RabiatS/MagicMitts/CAD Drawing/JN - Control Center/CC Proto K/JN - L1K Electromagnetic and String Housing.SLDPRT

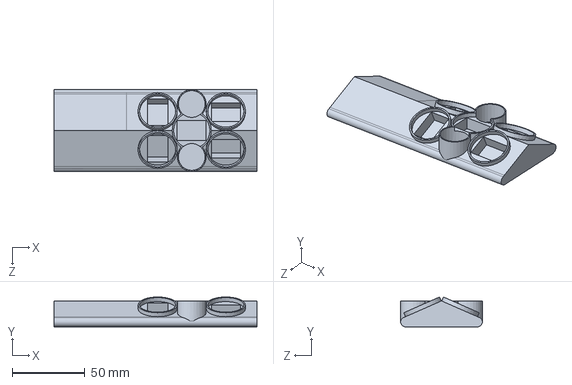
[picture p21: CAD file, 2025-01-15]
CAD Drawing/JN - Control Center/CC Proto K/JN - L1K Electromagnetic and String Housing.SLDPRT
140.0 x 20.7 x 56.4 mm
