RabiatS/MagicMitts/CAD Drawing/JN - Control Center/CC Proto L/JN - L1L Electromagnetic and String Housing.SLDPRT

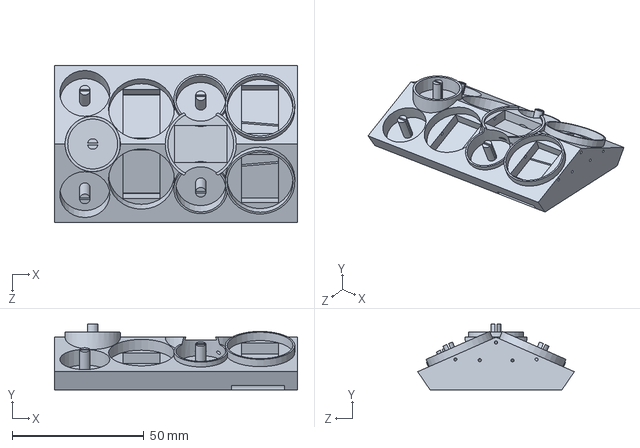
[picture p22: CAD file, 2025-01-15]
CAD Drawing/JN - Control Center/CC Proto L/JN - L1L Electromagnetic and String Housing.SLDPRT
92.2 x 25.0 x 59.4 mm
