RabiatS/MagicMitts/CAD Drawing/JN - Control Center/CC Proto M/JN - L1M Electromagnetic and String Housing.SLDPRT

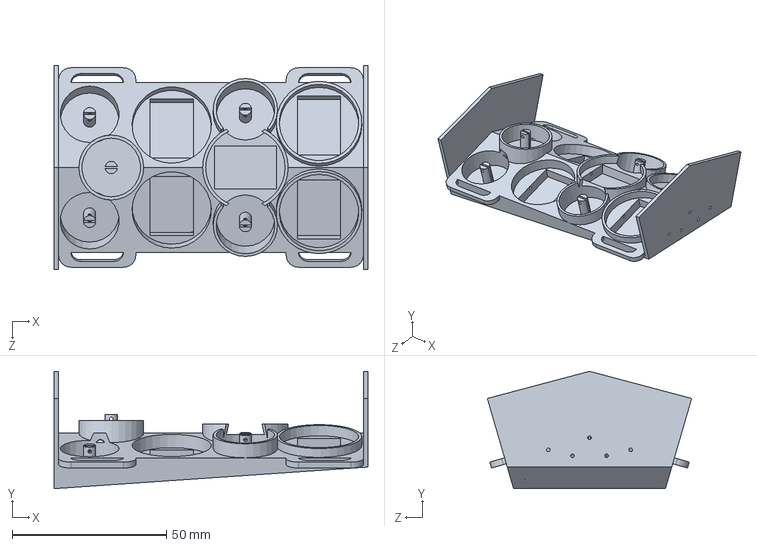
[picture p23: CAD file, 2025-01-15]
CAD Drawing/JN - Control Center/CC Proto M/JN - L1M Electromagnetic and String Housing.SLDPRT
101.7 x 38.0 x 66.2 mm
