RabiatS/MagicMitts/CAD Drawing/JN - Finger Caps and Tracks/JN - FCT Proto A/JN - Top Finger Cap - TFC-A.SLDPRT

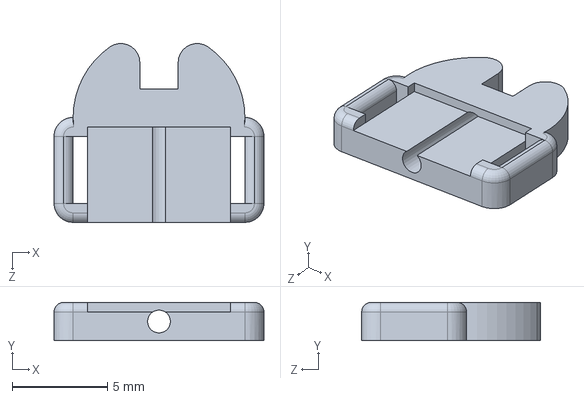
[picture p24: CAD file, 2025-01-15]
CAD Drawing/JN - Finger Caps and Tracks/JN - FCT Proto A/JN - Top Finger Cap - TFC-A.SLDPRT
11.0 x 2.00 x 9.37 mm
