RabiatS/MagicMitts/CAD Drawing/JN - Finger Caps and Tracks/JN - FCT Proto B/JN - Flex String Track - FST-B.SLDPRT

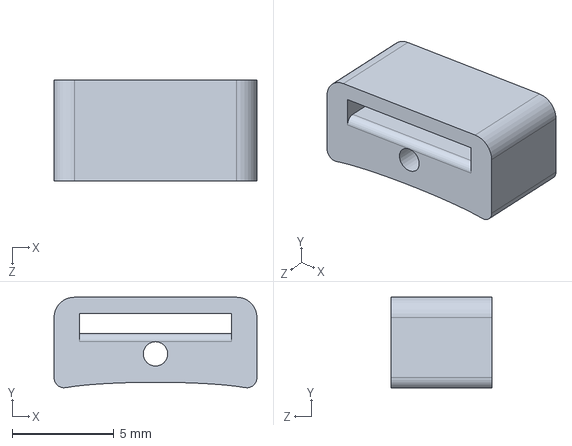
[picture p25: CAD file, 2025-01-15]
CAD Drawing/JN - Finger Caps and Tracks/JN - FCT Proto B/JN - Flex String Track - FST-B.SLDPRT
10.0 x 4.46 x 5.00 mm
