RabiatS/MagicMitts/CAD Drawing/JN - Reel Component Testing/JN - RC Testing 2/JN - Reel Caps Size2 T2.SLDPRT

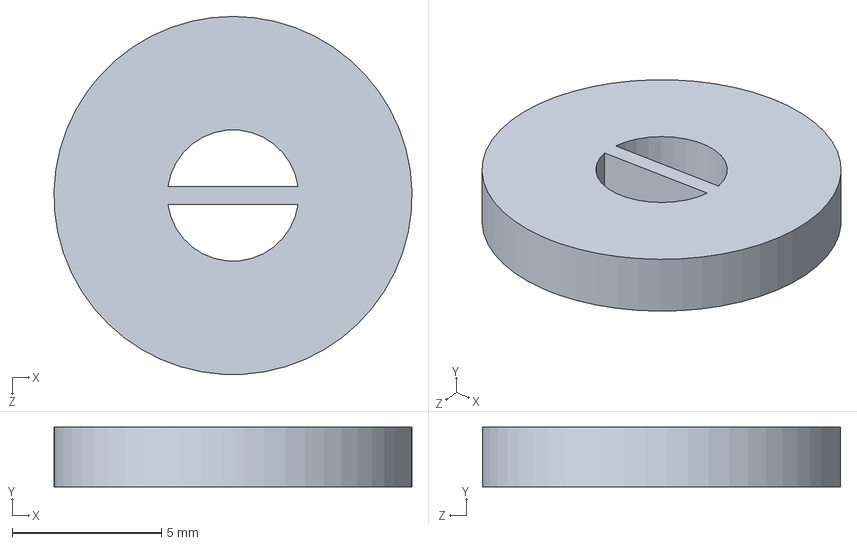
[picture p27: CAD file, 2025-01-15]
CAD Drawing/JN - Reel Component Testing/JN - RC Testing 2/JN - Reel Caps Size2 T2.SLDPRT
12.0 x 2.00 x 12.0 mm
