RabiatS/MagicMitts/CAD Drawing/BN - Battery Pack/BN - BP Proto A/BN - BP_BOTTOM A.STL

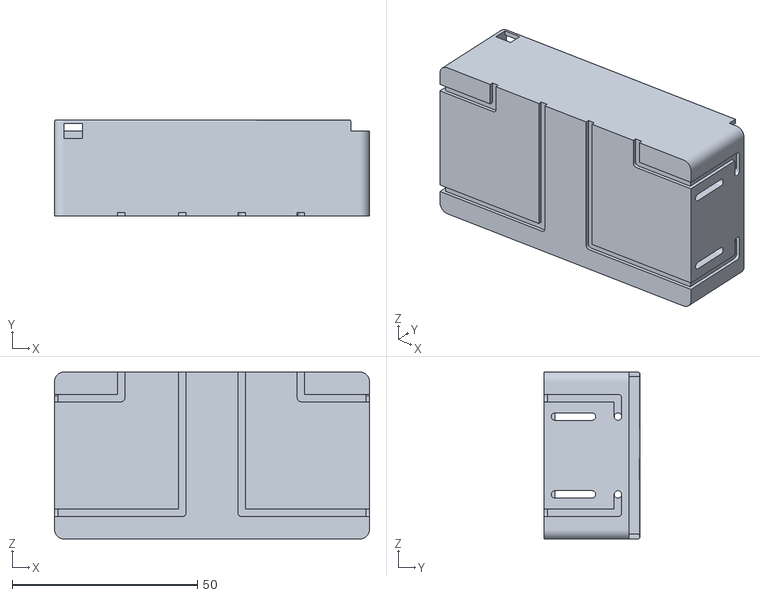
[picture p28: CAD file, 2025-01-15]
CAD Drawing/BN - Battery Pack/BN - BP Proto A/BN - BP_BOTTOM A.STL
85.0 x 26.0 x 45.0
