RabiatS/MagicMitts/CAD Drawing/BN - Battery Pack/BN - BP Proto B/BN - BP_LID B.STL

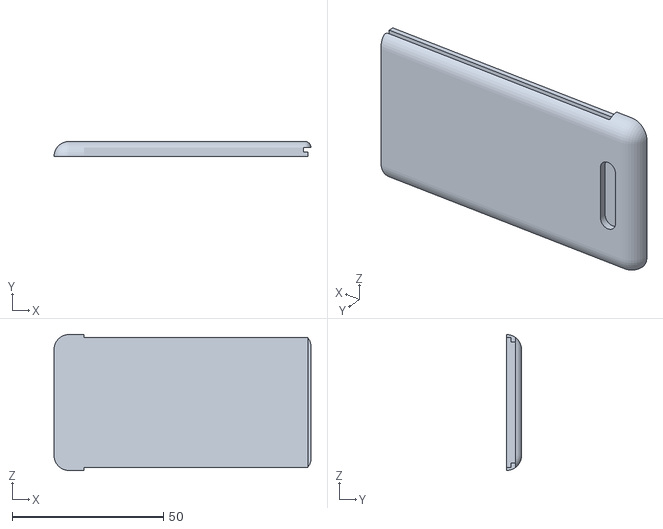
[picture p29: CAD file, 2025-01-15]
CAD Drawing/BN - Battery Pack/BN - BP Proto B/BN - BP_LID B.STL
85.0 x 5.00 x 45.0
