RabiatS/MagicMitts/CAD Drawing/JN - Ball Bearing Testing/JN - BB Testing 1/JN - Pole Size Testing Plate.SLDPRT

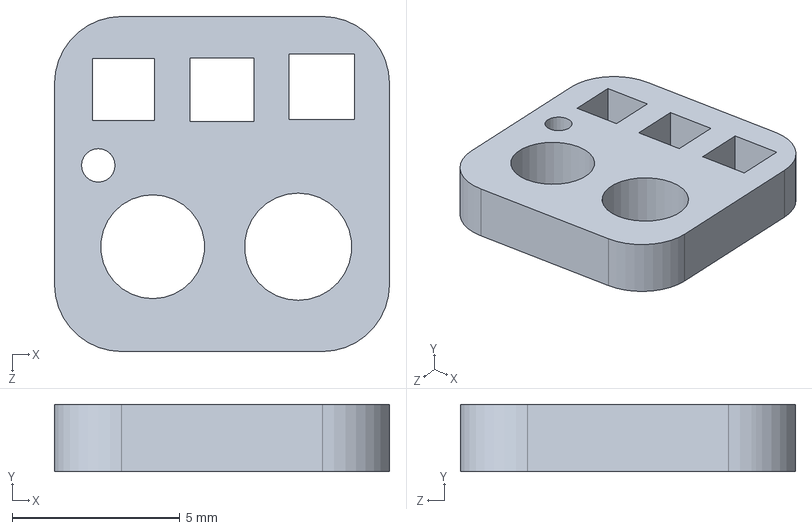
[picture p30: CAD file, 2025-01-15]
CAD Drawing/JN - Ball Bearing Testing/JN - BB Testing 1/JN - Pole Size Testing Plate.SLDPRT
10.00 x 2.00 x 10.0 mm
