RabiatS/MagicMitts/CAD Drawing/JN - Control Center/CC Proto B/JN - L3B Electromagnetic Housing Cap.SLDPRT

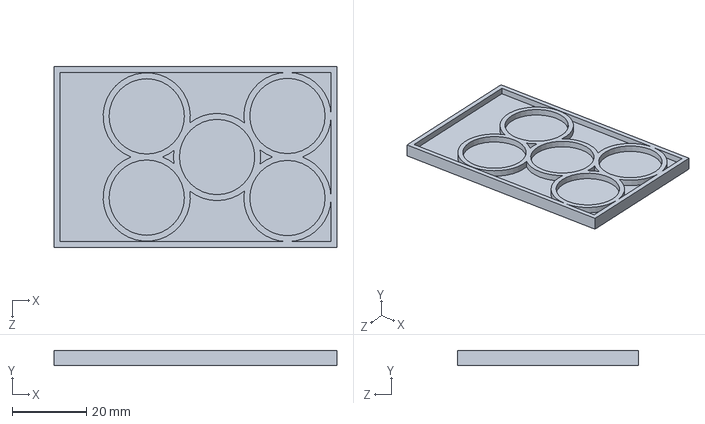
[picture p31: CAD file, 2025-01-15]
CAD Drawing/JN - Control Center/CC Proto B/JN - L3B Electromagnetic Housing Cap.SLDPRT
76.0 x 4.00 x 48.7 mm
