RabiatS/MagicMitts/CAD Drawing/JN - Control Center/CC Proto C/JN - TP L1C Electromagnetic and String.SLDPRT

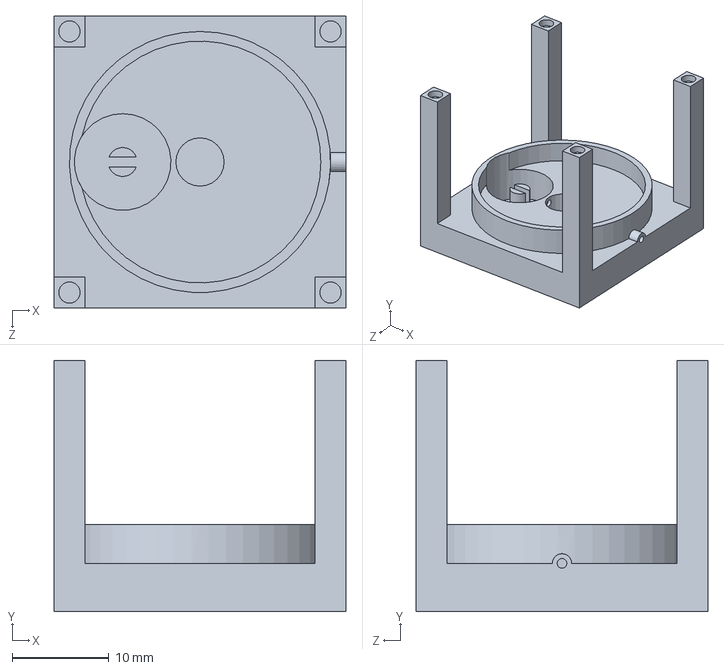
[picture p32: CAD file, 2025-01-15]
CAD Drawing/JN - Control Center/CC Proto C/JN - TP L1C Electromagnetic and String.SLDPRT
30.2 x 26.0 x 30.2 mm
