RabiatS/MagicMitts/CAD Drawing/JN - Control Center/CC Proto D/JN - LD Badge Reel Component.SLDPRT

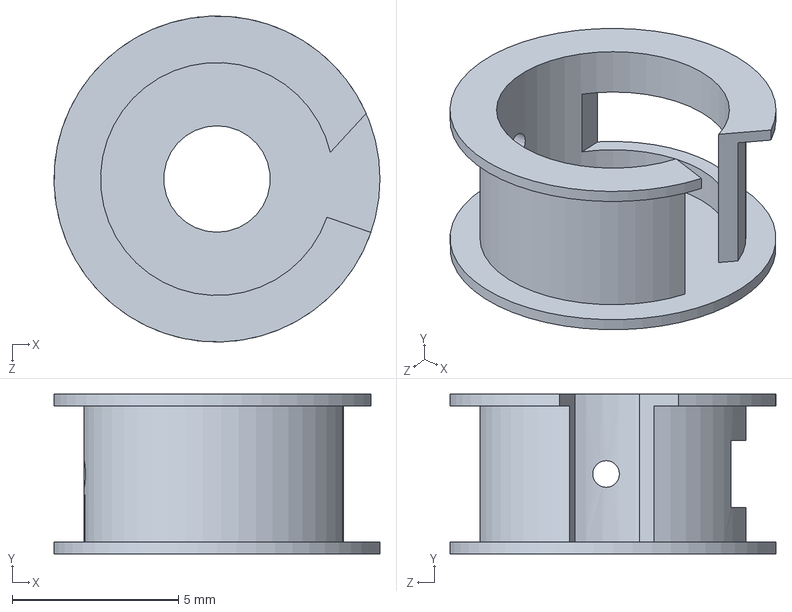
[picture p33: CAD file, 2025-01-15]
CAD Drawing/JN - Control Center/CC Proto D/JN - LD Badge Reel Component.SLDPRT
9.80 x 4.80 x 9.80 mm
