RabiatS/MagicMitts/CAD Drawing/JN - Control Center/CC Proto E/JN - TP L1E Electromagnetic and String Housing.SLDPRT

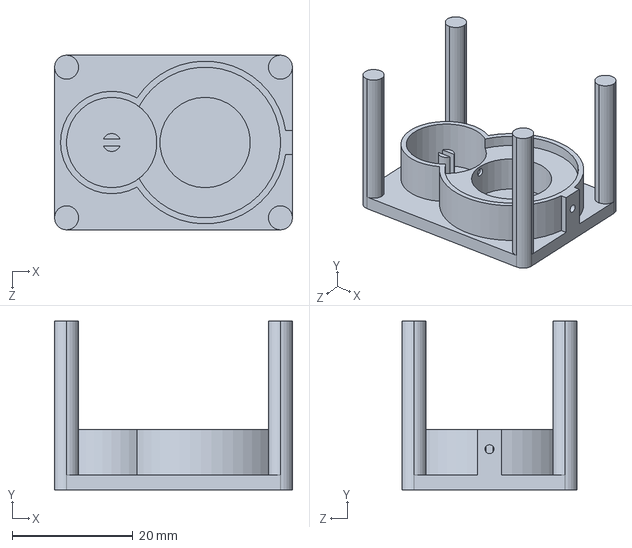
[picture p34: CAD file, 2025-01-15]
CAD Drawing/JN - Control Center/CC Proto E/JN - TP L1E Electromagnetic and String Housing.SLDPRT
39.5 x 28.0 x 29.0 mm
