RabiatS/MagicMitts/CAD Drawing/JN - Control Center/CC Proto G/JN - TP L2G Cap.SLDPRT

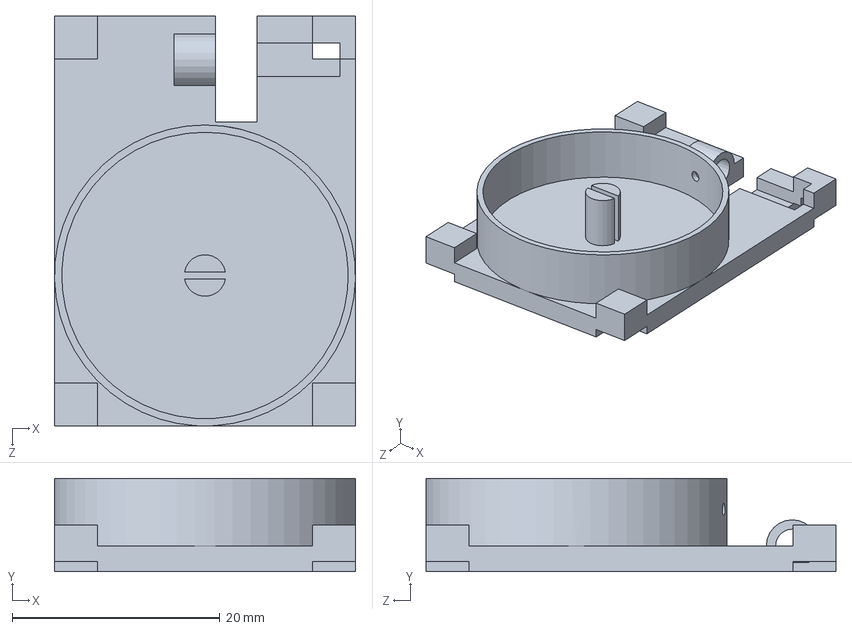
[picture p35: CAD file, 2025-01-15]
CAD Drawing/JN - Control Center/CC Proto G/JN - TP L2G Cap.SLDPRT
29.0 x 9.00 x 39.5 mm
