RabiatS/MagicMitts/CAD Drawing/JN - Control Center/CC Proto H/JN - TP L1H Badge Reel Cap.SLDPRT

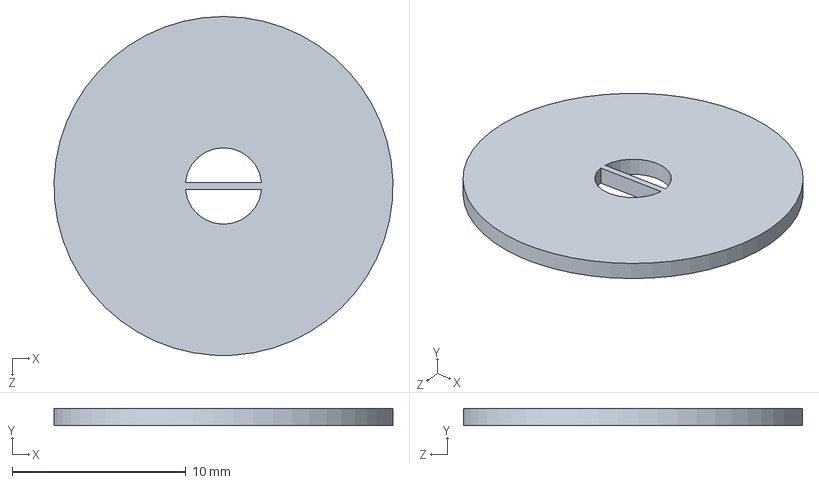
[picture p36: CAD file, 2025-01-15]
CAD Drawing/JN - Control Center/CC Proto H/JN - TP L1H Badge Reel Cap.SLDPRT
19.5 x 1.00 x 19.5 mm
