RabiatS/MagicMitts/CAD Drawing/JN - Control Center/CC Proto J/JN - L1J Electromagnetic and String Housing.SLDPRT

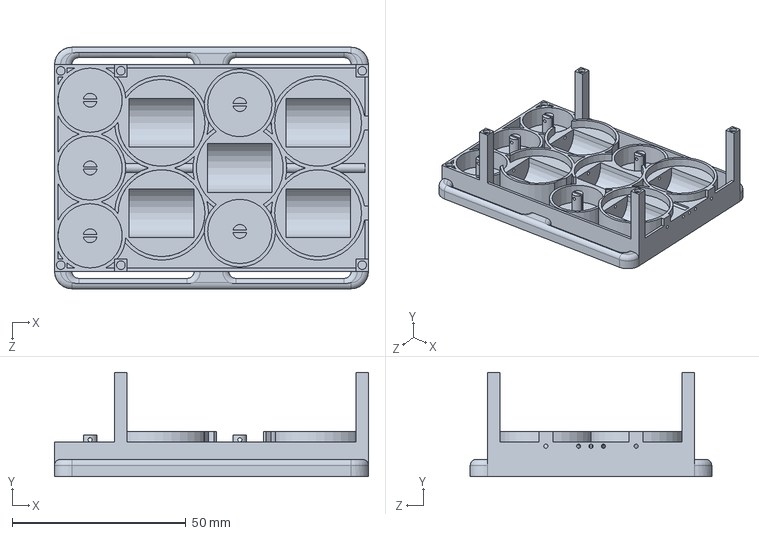
[picture p37: CAD file, 2025-01-15]
CAD Drawing/JN - Control Center/CC Proto J/JN - L1J Electromagnetic and String Housing.SLDPRT
90.3 x 30.0 x 69.5 mm
