RabiatS/MagicMitts/CAD Drawing/JN - Finger Caps and Tracks/JN - FCT Proto A/JN - Flex String Track - FST-A.SLDPRT

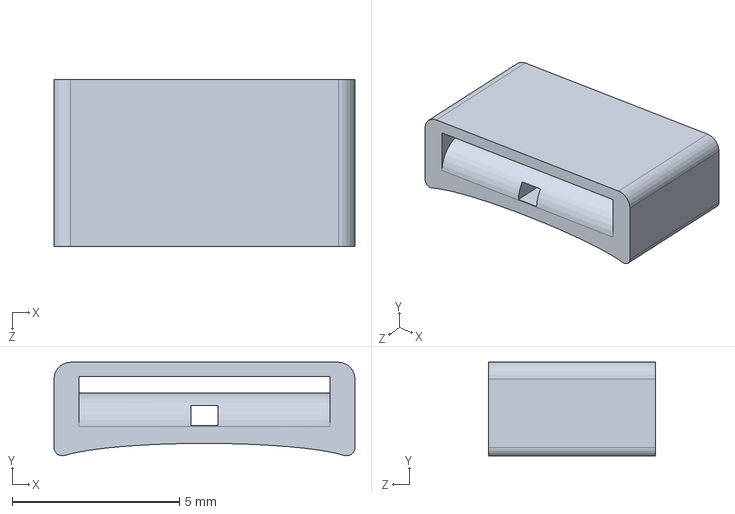
[picture p38: CAD file, 2025-01-15]
CAD Drawing/JN - Finger Caps and Tracks/JN - FCT Proto A/JN - Flex String Track - FST-A.SLDPRT
9.00 x 2.80 x 5.00 mm
