RabiatS/MagicMitts/CAD Drawing/JN - Reel Component Testing/JN - RC Testing 1/JN - Reel Housing T1.SLDPRT

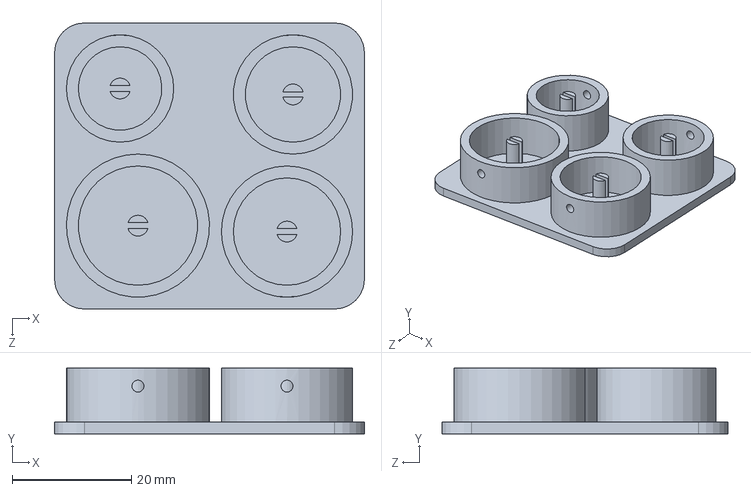
[picture p40: CAD file, 2025-01-15]
CAD Drawing/JN - Reel Component Testing/JN - RC Testing 1/JN - Reel Housing T1.SLDPRT
52.0 x 11.0 x 48.0 mm
