RabiatS/MagicMitts/CAD Drawing/JN - Ball Bearing Testing/JN - BB Testing 1/JN - Bearing Pole 1.5R.SLDPRT

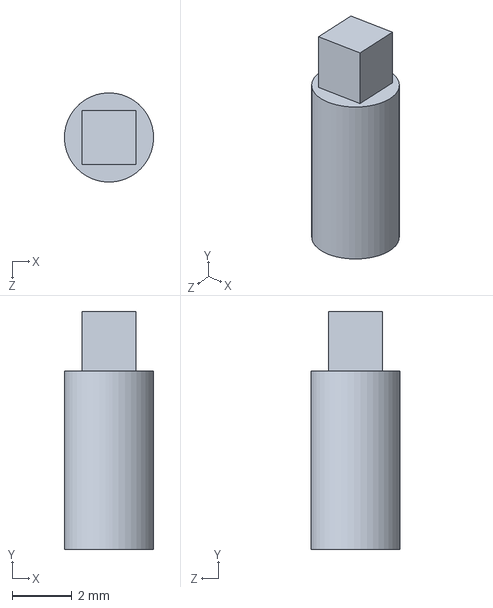
[picture p42: CAD file, 2025-01-15]
CAD Drawing/JN - Ball Bearing Testing/JN - BB Testing 1/JN - Bearing Pole 1.5R.SLDPRT
3.00 x 8.00 x 3.00 mm
