RabiatS/MagicMitts/CAD Drawing/JN - Control Center/CC Proto A/JN - Electromagnetic Housing.SLDPRT

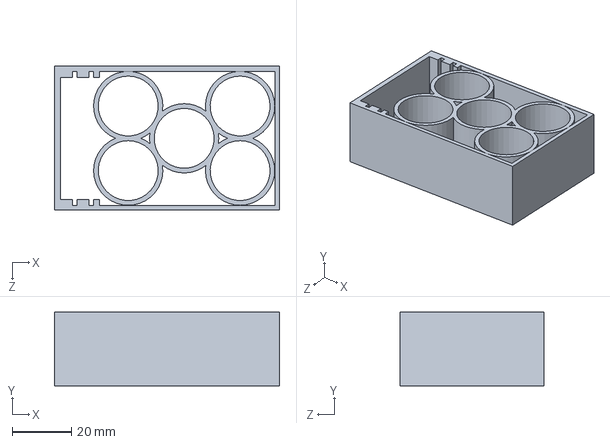
[picture p43: CAD file, 2025-01-15]
CAD Drawing/JN - Control Center/CC Proto A/JN - Electromagnetic Housing.SLDPRT
76.0 x 25.0 x 48.7 mm
