RabiatS/MagicMitts/CAD Drawing/JN - Control Center/CC Proto B/JN - L1B Bottom String Circuit.SLDPRT

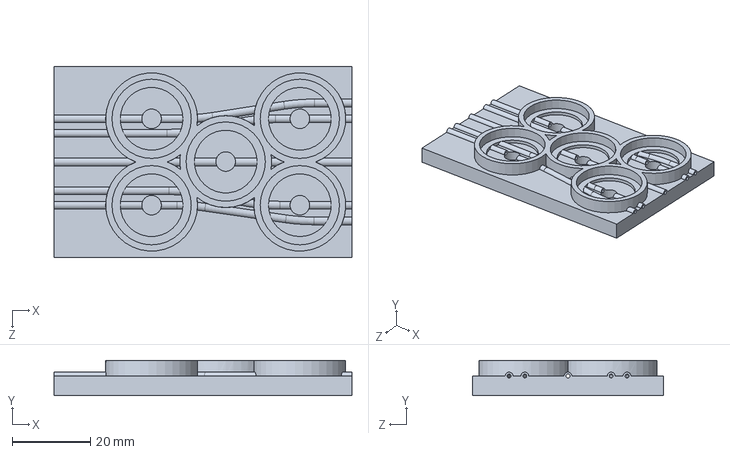
[picture p44: CAD file, 2025-01-15]
CAD Drawing/JN - Control Center/CC Proto B/JN - L1B Bottom String Circuit.SLDPRT
76.0 x 9.00 x 48.7 mm
