RabiatS/MagicMitts/CAD Drawing/JN - Control Center/CC Proto D/JN - L1D Test Part.SLDPRT

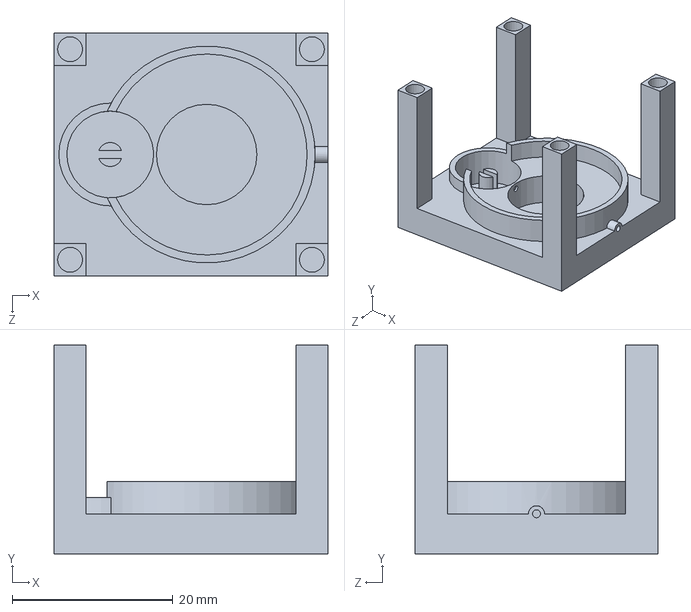
[picture p45: CAD file, 2025-01-15]
CAD Drawing/JN - Control Center/CC Proto D/JN - L1D Test Part.SLDPRT
34.1 x 26.0 x 30.2 mm
