RabiatS/MagicMitts/CAD Drawing/JN - Control Center/CC Proto E/JN - LE Badge Reel Component.SLDPRT

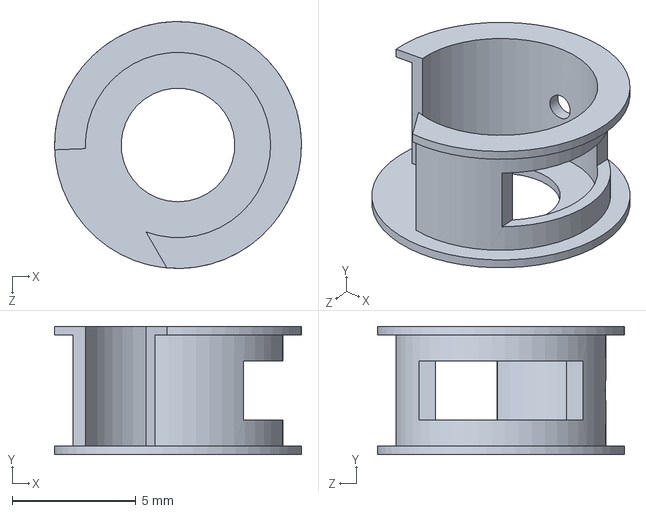
[picture p46: CAD file, 2025-01-15]
CAD Drawing/JN - Control Center/CC Proto E/JN - LE Badge Reel Component.SLDPRT
10.00 x 5.20 x 10.0 mm
