RabiatS/MagicMitts/CAD Drawing/JN - Control Center/CC Proto G/JN - TP L2G Bearing Pole.SLDPRT

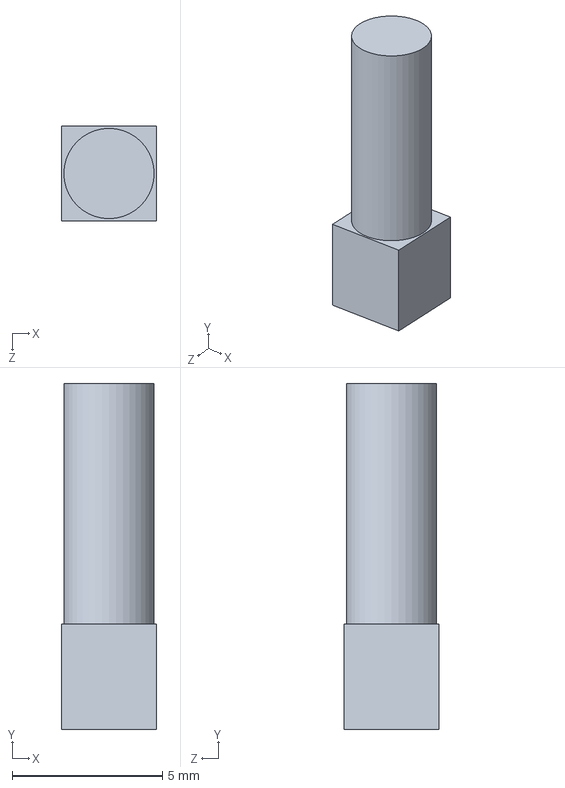
[picture p47: CAD file, 2025-01-15]
CAD Drawing/JN - Control Center/CC Proto G/JN - TP L2G Bearing Pole.SLDPRT
3.15 x 11.5 x 3.15 mm
