RabiatS/MagicMitts/CAD Drawing/JN - Control Center/CC Proto H/JN - TP L1H Electromagnetic and String Housing.SLDPRT

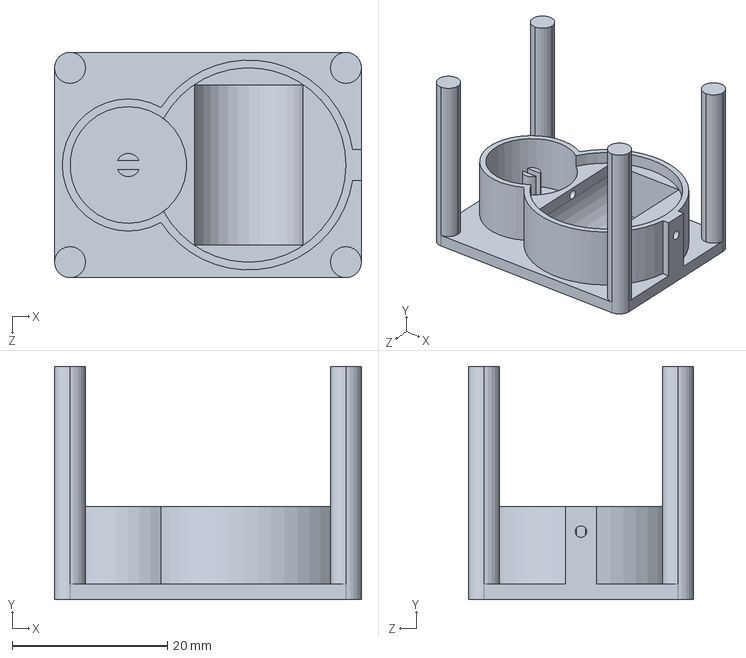
[picture p48: CAD file, 2025-01-15]
CAD Drawing/JN - Control Center/CC Proto H/JN - TP L1H Electromagnetic and String Housing.SLDPRT
39.5 x 30.0 x 29.0 mm
