RabiatS/MagicMitts/CAD Drawing/JN - Control Center/CC Proto J/JN - L2J Electromagnetic Housing Cap.SLDPRT

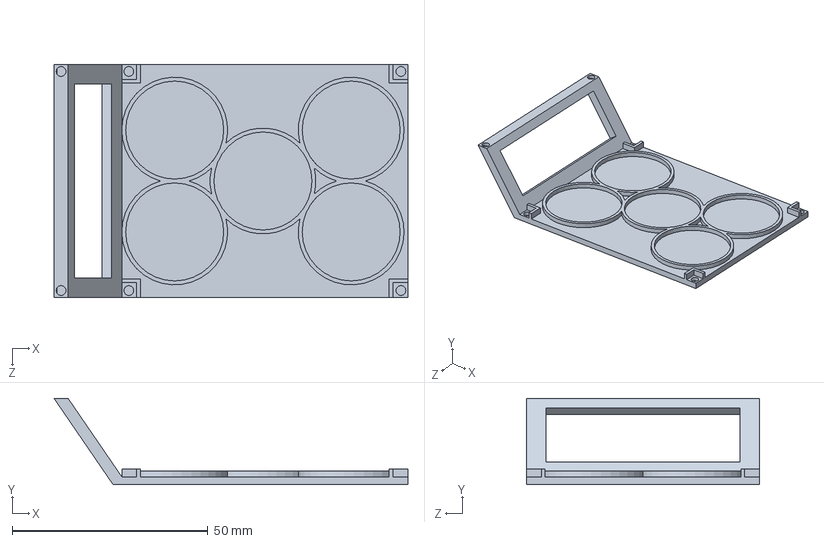
[picture p49: CAD file, 2025-01-15]
CAD Drawing/JN - Control Center/CC Proto J/JN - L2J Electromagnetic Housing Cap.SLDPRT
90.3 x 22.0 x 59.5 mm
