RabiatS/MagicMitts/CAD Drawing/JN - Finger Caps and Tracks/JN - FCT Proto A/JN - Bottom Finger Cap - BFC-A.SLDPRT

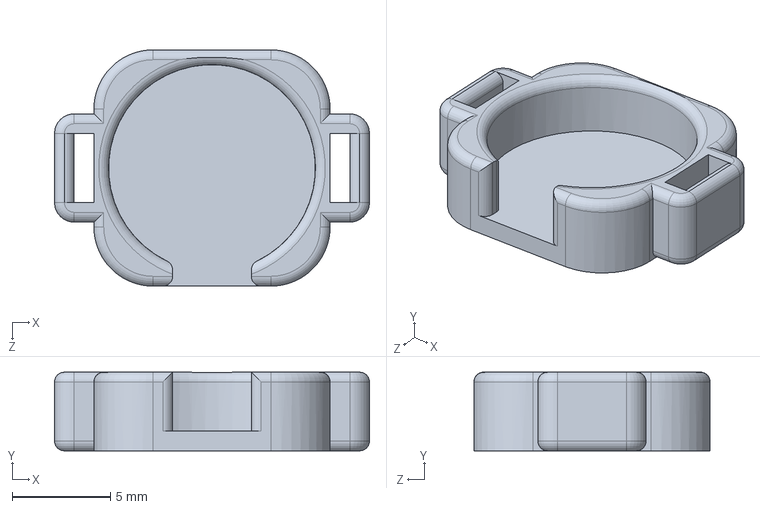
[picture p50: CAD file, 2025-01-15]
CAD Drawing/JN - Finger Caps and Tracks/JN - FCT Proto A/JN - Bottom Finger Cap - BFC-A.SLDPRT
16.0 x 4.00 x 12.0 mm
