RabiatS/MagicMitts/CAD Drawing/JN - Finger Caps and Tracks/JN - FCT Proto B/JN - Top Finger Cap - TFC-B.SLDPRT

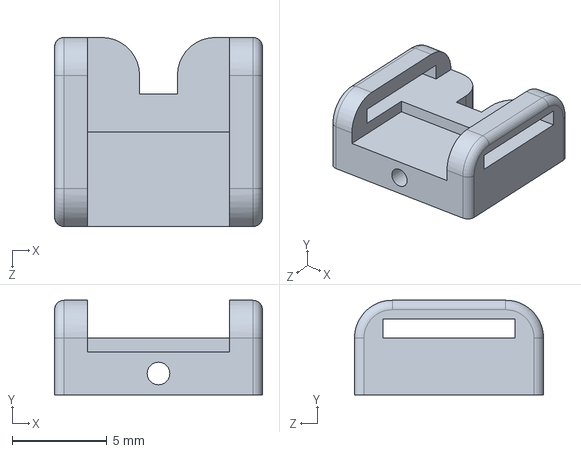
[picture p51: CAD file, 2025-01-15]
CAD Drawing/JN - Finger Caps and Tracks/JN - FCT Proto B/JN - Top Finger Cap - TFC-B.SLDPRT
11.0 x 5.00 x 10.0 mm
