RabiatS/MagicMitts/CAD Drawing/JN - Reel Component Testing/JN - RC Testing 1/JN - Reel Caps T1.SLDPRT

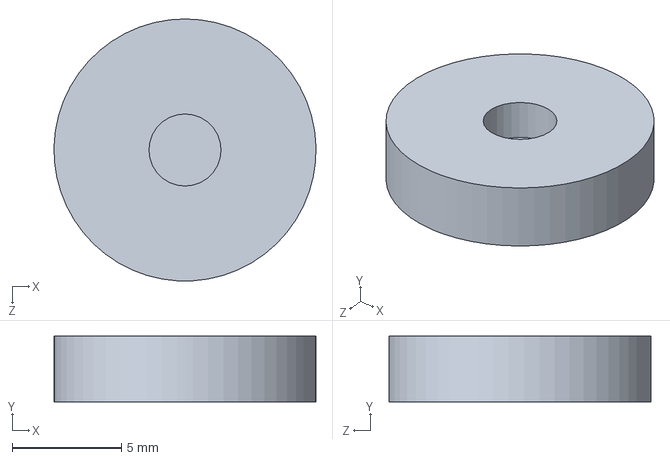
[picture p52: CAD file, 2025-01-15]
CAD Drawing/JN - Reel Component Testing/JN - RC Testing 1/JN - Reel Caps T1.SLDPRT
12.0 x 3.00 x 12.0 mm
