RabiatS/MagicMitts/CAD Drawing/JN - Reel Component Testing/JN - RC Testing 2/JN - Reel Housing T2.SLDPRT

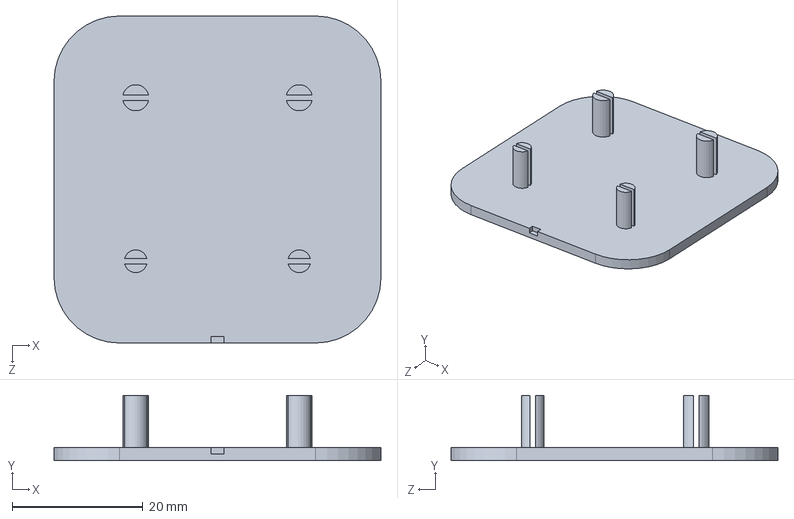
[picture p53: CAD file, 2025-01-15]
CAD Drawing/JN - Reel Component Testing/JN - RC Testing 2/JN - Reel Housing T2.SLDPRT
50.0 x 10.0 x 50.0 mm
