RabiatS/MagicMitts/CAD Drawing/JN - Control Center/CC Proto H/JN - TP L1H Badge Reel Holder.SLDPRT

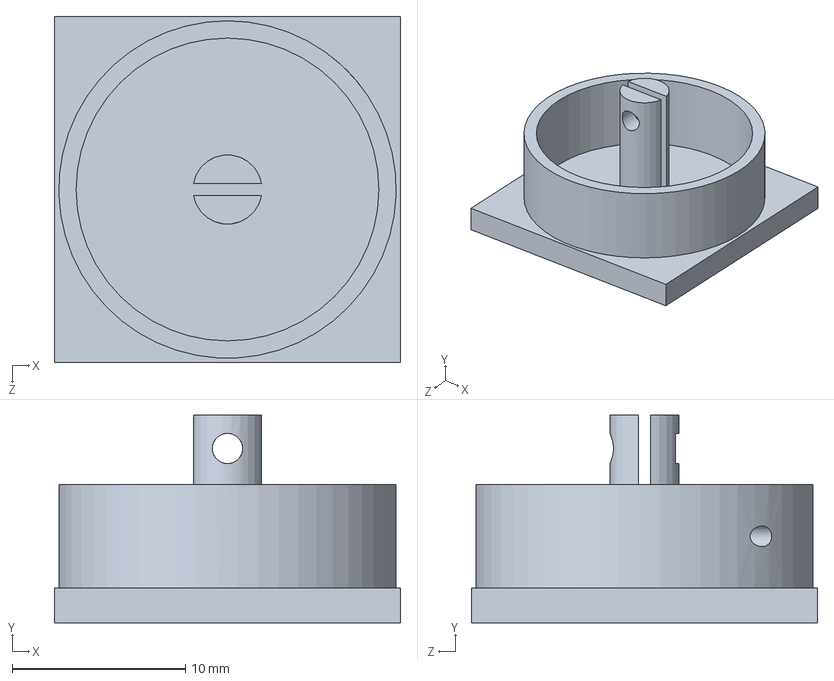
[picture p54: CAD file, 2025-01-15]
CAD Drawing/JN - Control Center/CC Proto H/JN - TP L1H Badge Reel Holder.SLDPRT
20.0 x 12.0 x 20.0 mm
