RabiatS/MagicMitts/CAD Drawing/JN - Reel Component Testing/JN - RC Testing 1/JN - S2 Reel T1.1.SLDPRT

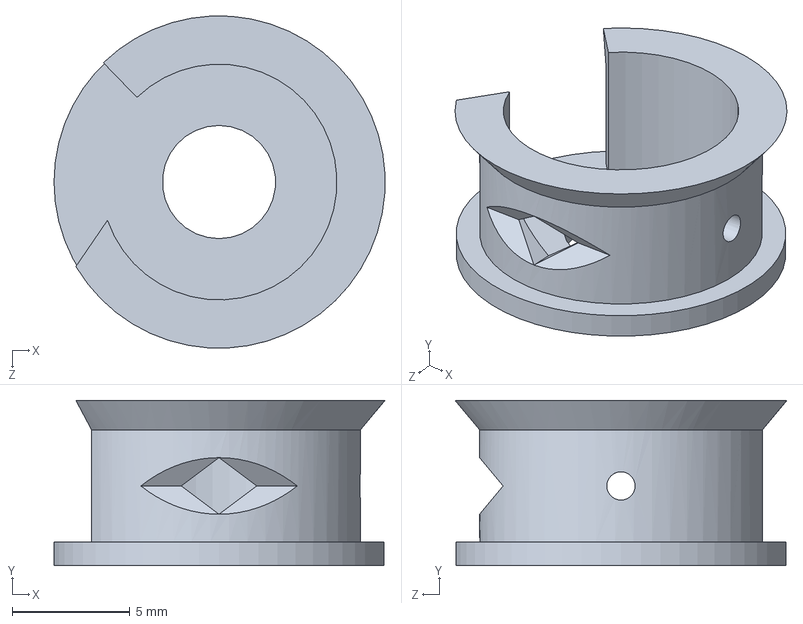
[picture p55: CAD file, 2025-01-15]
CAD Drawing/JN - Reel Component Testing/JN - RC Testing 1/JN - S2 Reel T1.1.SLDPRT
14.0 x 7.00 x 14.1 mm
