RabiatS/MagicMitts/CAD Drawing/JN - Control Center/CC Proto C/JN - TP L2C Electromagnetic Cap.SLDPRT

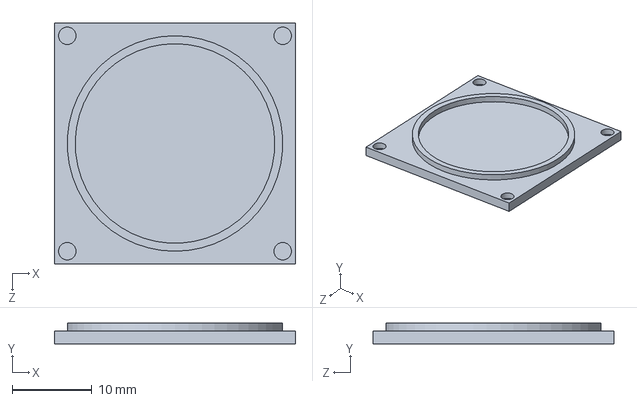
[picture p56: CAD file, 2025-01-15]
CAD Drawing/JN - Control Center/CC Proto C/JN - TP L2C Electromagnetic Cap.SLDPRT
30.2 x 2.60 x 30.2 mm
