RabiatS/MagicMitts/CAD Drawing/JN - Reel Component Testing/JN - RC Testing 1/JN - S3 Reel T1.SLDPRT

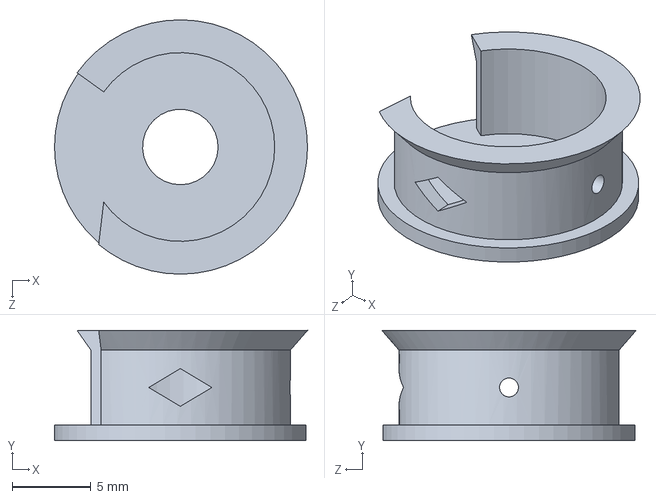
[picture p57: CAD file, 2025-01-15]
CAD Drawing/JN - Reel Component Testing/JN - RC Testing 1/JN - S3 Reel T1.SLDPRT
16.1 x 7.00 x 16.2 mm
